Susssiest/Nornir-Chest-Project/All CAD/All STEPS/Stalagmite_2.step

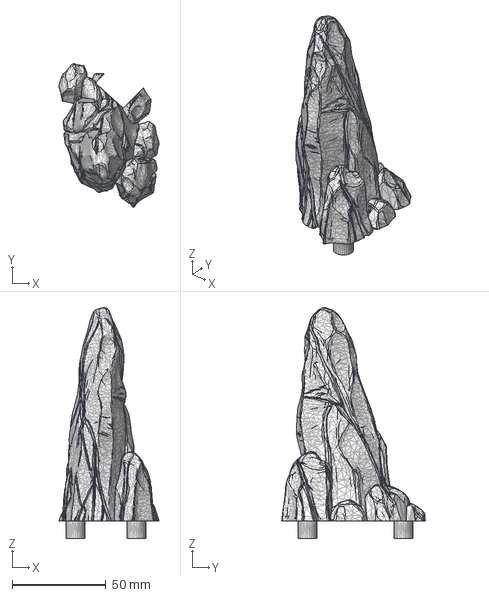
[picture p15: CAD file, 2026-08-25]
All CAD/All STEPS/Stalagmite_2.step
53.3 x 76.5 x 123.0 mm
