Susssiest/Nornir-Chest-Project/All CAD/All STEPS/Rune_Cylinder.step

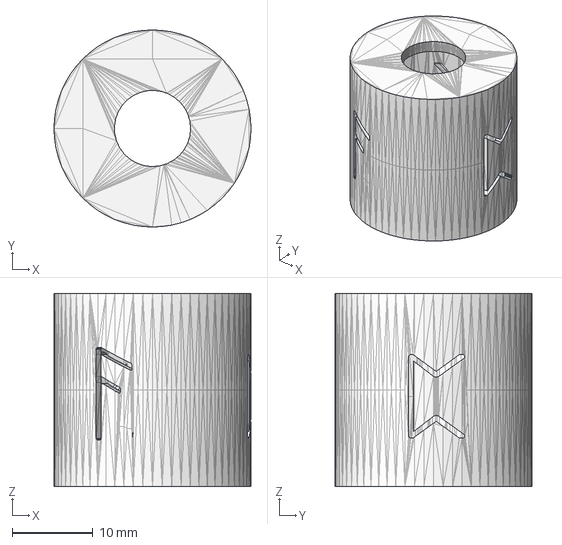
[picture p16: CAD file, 2026-08-25]
All CAD/All STEPS/Rune_Cylinder.step
24.4 x 24.4 x 23.9 mm
