Susssiest/Nornir-Chest-Project/All CAD/All STEPS/LED_Cover_(Totem_Pole).step

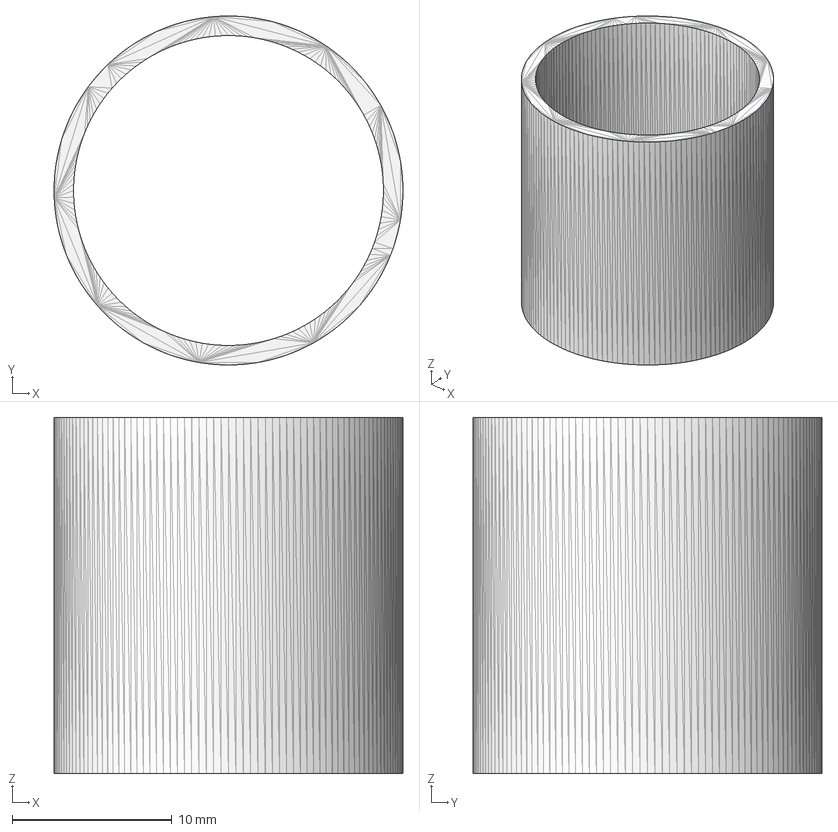
[picture p17: CAD file, 2026-08-25]
All CAD/All STEPS/LED_Cover_(Totem_Pole).step
21.8 x 21.8 x 22.3 mm
