Susssiest/Nornir-Chest-Project/All CAD/All STEPS/Totem_Pole.step

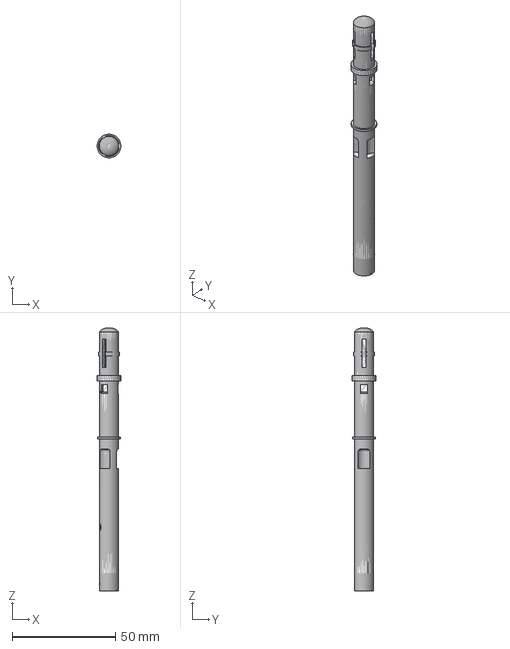
[picture p18: CAD file, 2026-08-25]
All CAD/All STEPS/Totem_Pole.step
11.5 x 11.5 x 127.4 mm
