Susssiest/Nornir-Chest-Project/All CAD/All STEPS/Gold_Engraving_Long PRINT_4.step

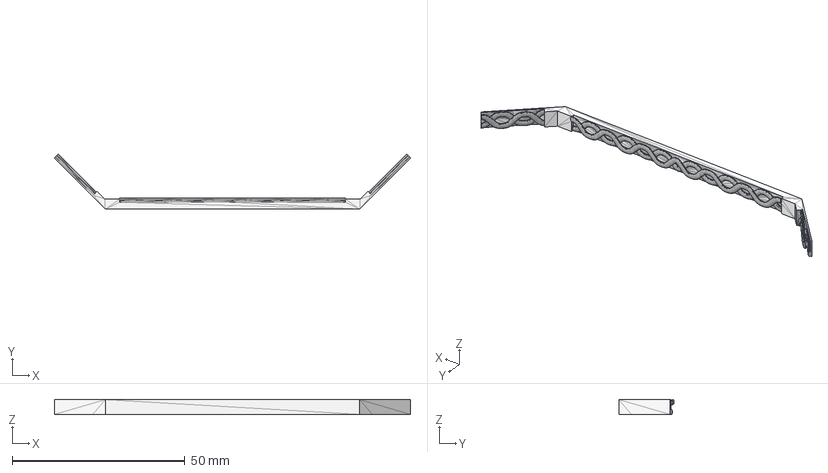
[picture p19: CAD file, 2026-08-25]
All CAD/All STEPS/Gold_Engraving_Long PRINT_4.step
103.2 x 16.0 x 4.30 mm
