Susssiest/Nornir-Chest-Project/All CAD/All STEPS/Hing_PRINT_2.step

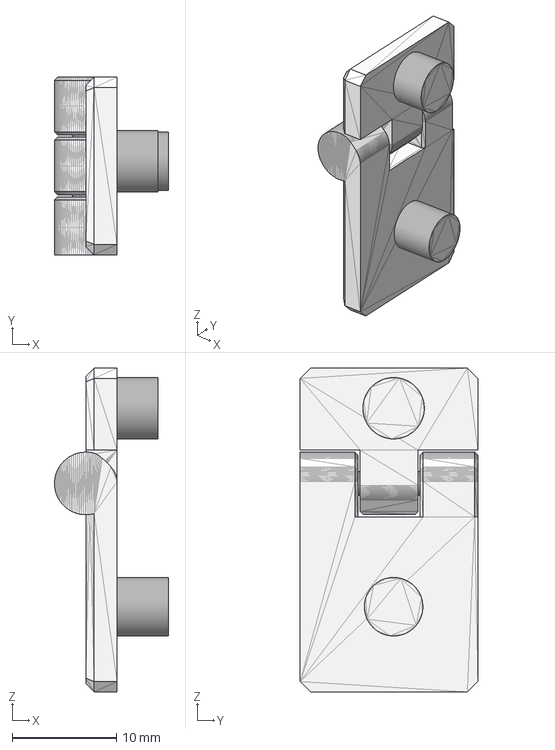
[picture p20: CAD file, 2026-08-25]
All CAD/All STEPS/Hing_PRINT_2.step
10.9 x 17.0 x 31.1 mm
