Susssiest/Nornir-Chest-Project/All CAD/All STEPS/Brazier_Rune_(R).step

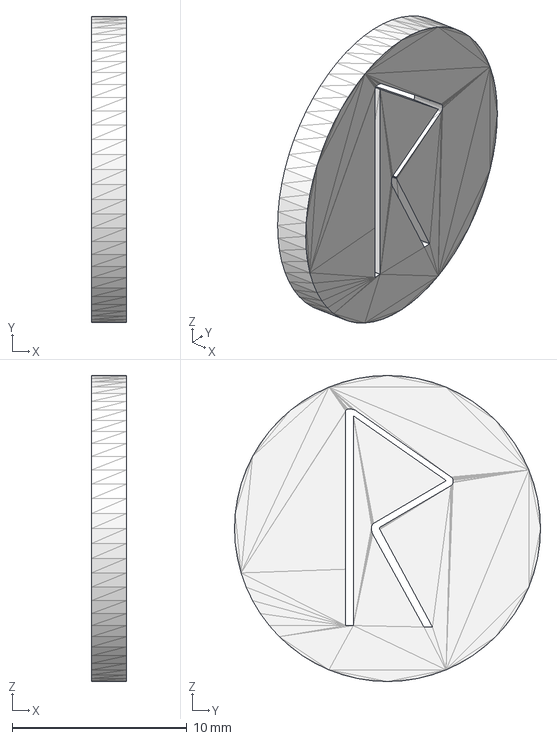
[picture p21: CAD file, 2026-08-25]
All CAD/All STEPS/Brazier_Rune_(R).step
2.00 x 17.5 x 17.5 mm
