Susssiest/Nornir-Chest-Project/All CAD/All STEPS/Base_Cover.step

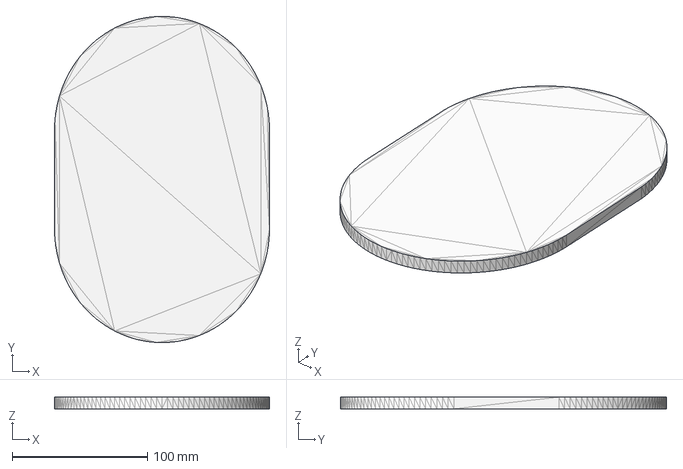
[picture p22: CAD file, 2026-08-25]
All CAD/All STEPS/Base_Cover.step
158.7 x 240.8 x 8.63 mm
