Susssiest/Nornir-Chest-Project/All CAD/All STEPS/Base_4.step

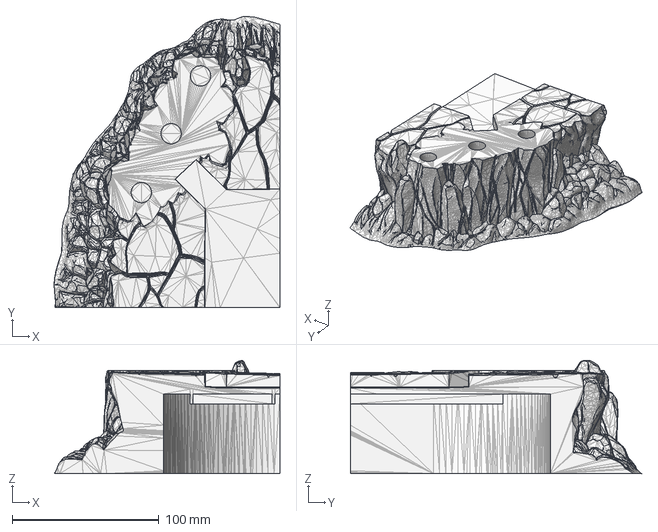
[picture p23: CAD file, 2026-08-25]
All CAD/All STEPS/Base_4.step
154.1 x 198.7 x 77.3 mm
