Susssiest/Nornir-Chest-Project/All CAD/All STEPS/Gold_Engraving_(Lid).step

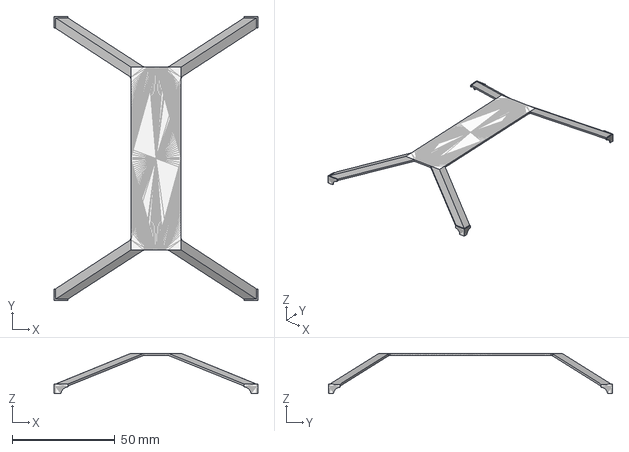
[picture p24: CAD file, 2026-08-25]
All CAD/All STEPS/Gold_Engraving_(Lid).step
99.3 x 138.4 x 19.7 mm
