Susssiest/Nornir-Chest-Project/All CAD/All STEPS/Lid.step

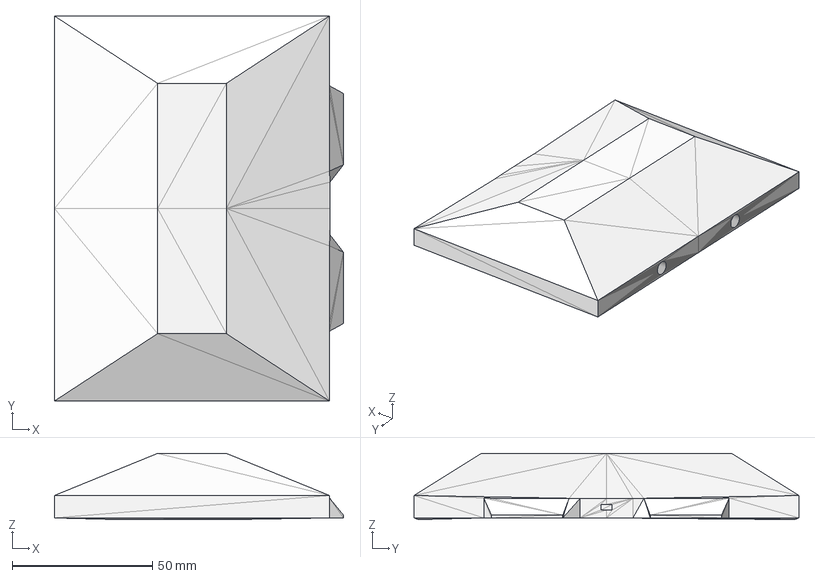
[picture p25: CAD file, 2026-08-25]
All CAD/All STEPS/Lid.step
103.0 x 137.2 x 23.6 mm
