Susssiest/Nornir-Chest-Project/All CAD/All STEPS/Pole_Target Print_3.step

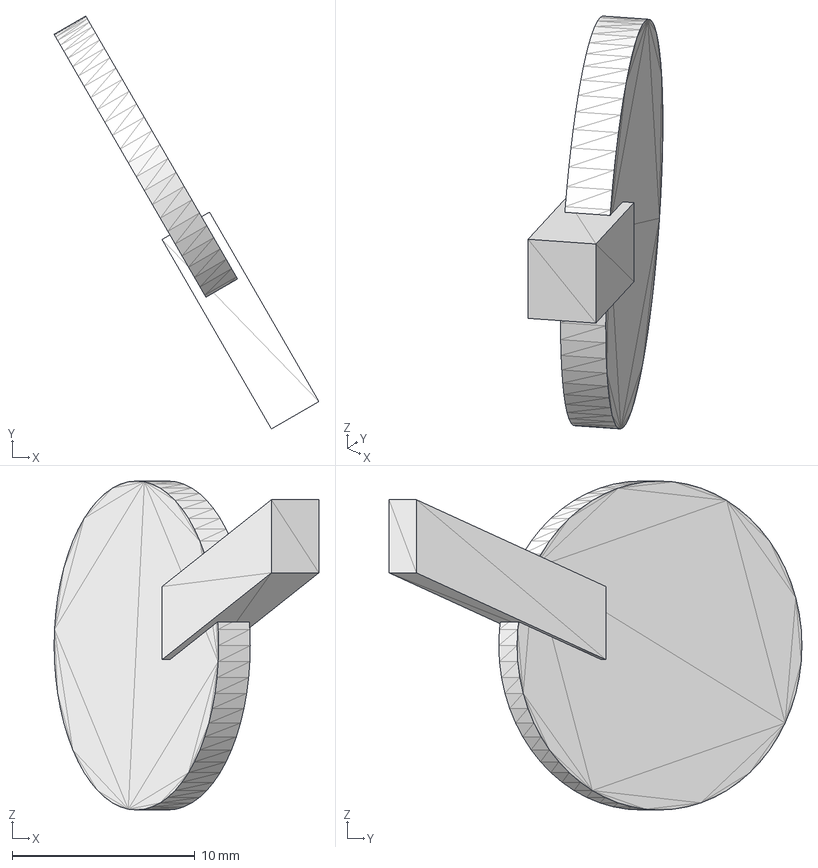
[picture p26: CAD file, 2026-08-25]
All CAD/All STEPS/Pole_Target Print_3.step
14.5 x 22.6 x 18.0 mm
