Susssiest/Nornir-Chest-Project/All CAD/All STEPS/Electronics_Cover.step

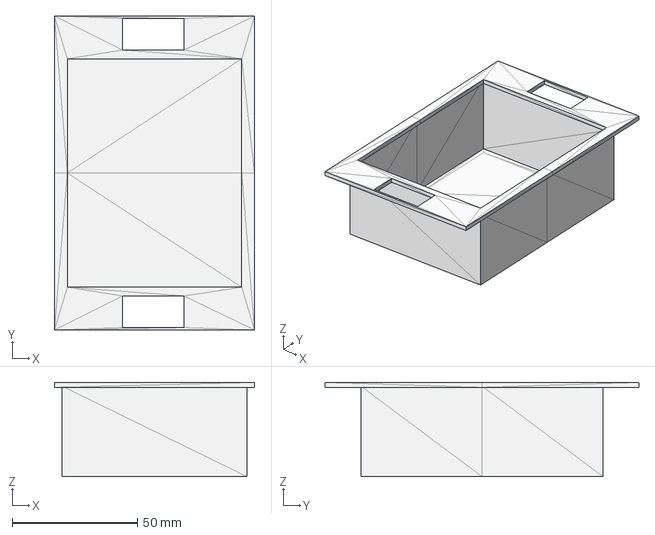
[picture p27: CAD file, 2026-08-25]
All CAD/All STEPS/Electronics_Cover.step
79.9 x 125.4 x 37.7 mm
