Susssiest/Nornir-Chest-Project/All CAD/All STEPS/Led_Cover_Print_3.step

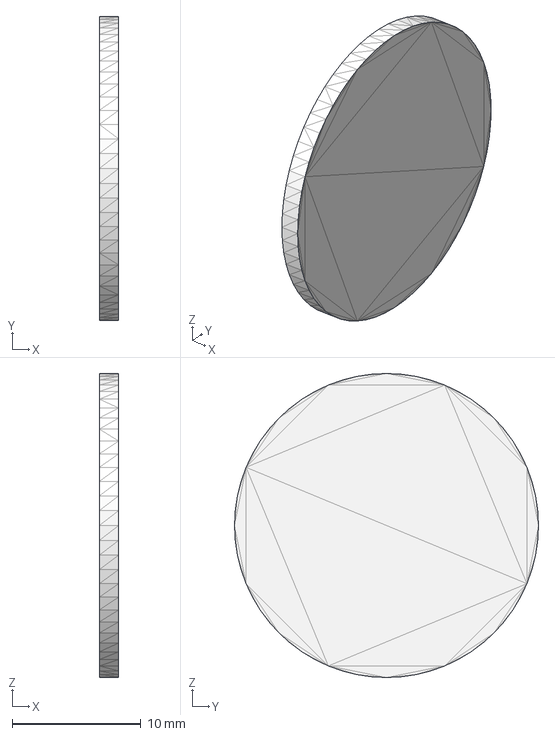
[picture p28: CAD file, 2026-08-25]
All CAD/All STEPS/Led_Cover_Print_3.step
1.50 x 23.6 x 23.6 mm
