Susssiest/Nornir-Chest-Project/All CAD/All STEPS/Ring_Print_3.step

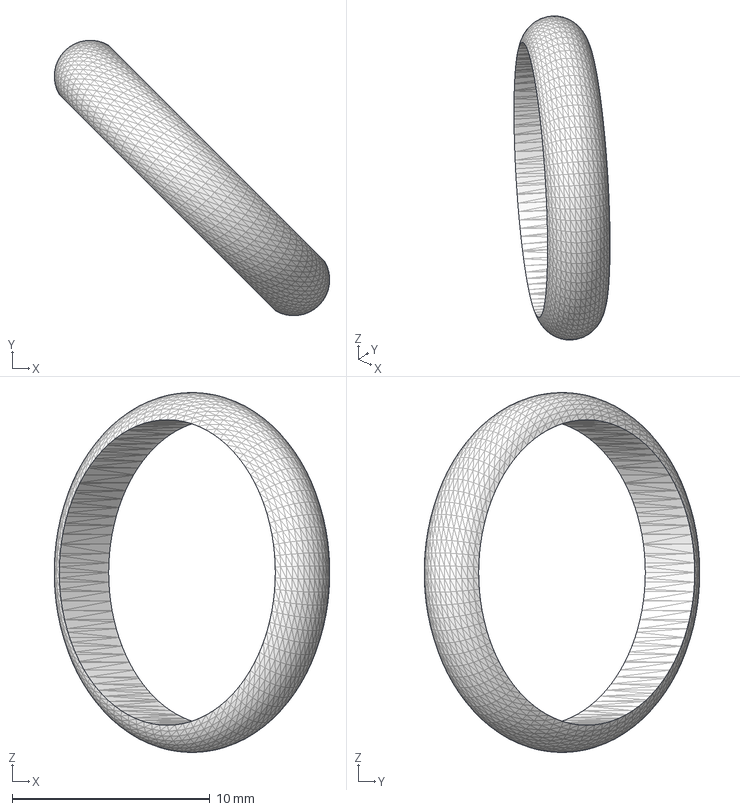
[picture p29: CAD file, 2026-08-25]
All CAD/All STEPS/Ring_Print_3.step
13.9 x 13.9 x 18.2 mm
