Susssiest/Nornir-Chest-Project/All CAD/All STEPS/Bottom.step

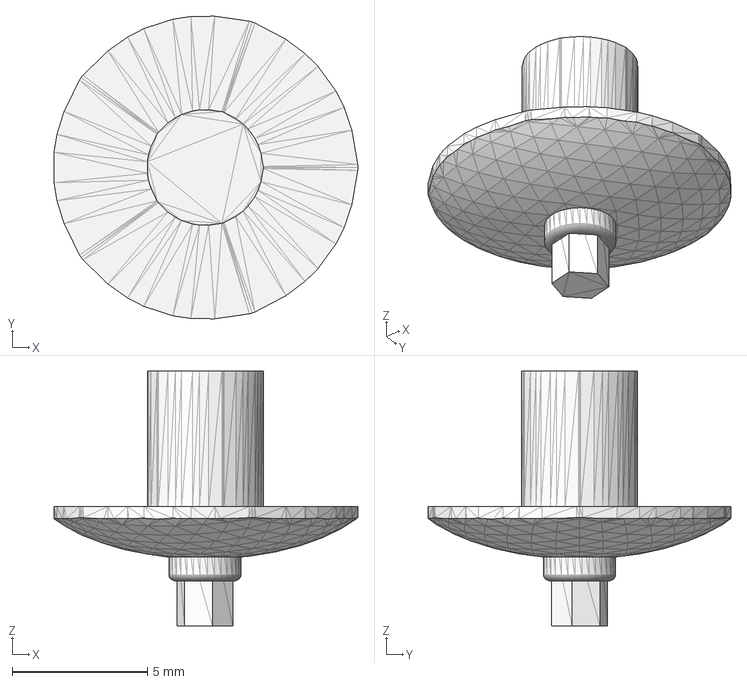
[picture p30: CAD file, 2026-08-25]
All CAD/All STEPS/Bottom.step
11.2 x 11.2 x 9.42 mm
