Susssiest/Nornir-Chest-Project/All CAD/All STEPS/Bell_Support.step

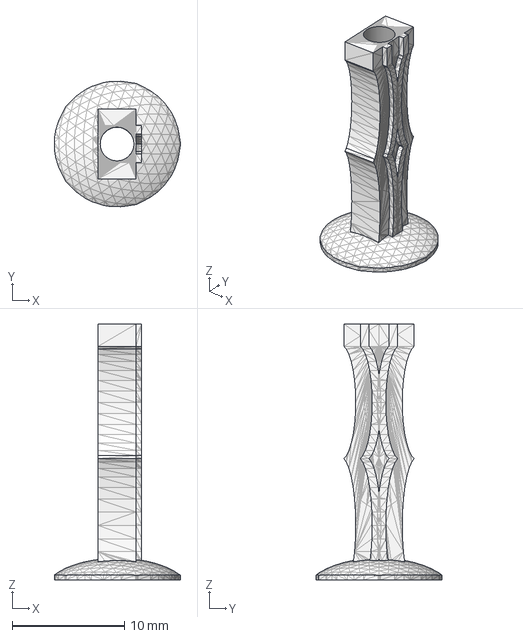
[picture p31: CAD file, 2026-08-25]
All CAD/All STEPS/Bell_Support.step
11.2 x 11.2 x 22.8 mm
