Susssiest/Nornir-Chest-Project/All CAD/All STEPS/Bell_Rune_(N).step

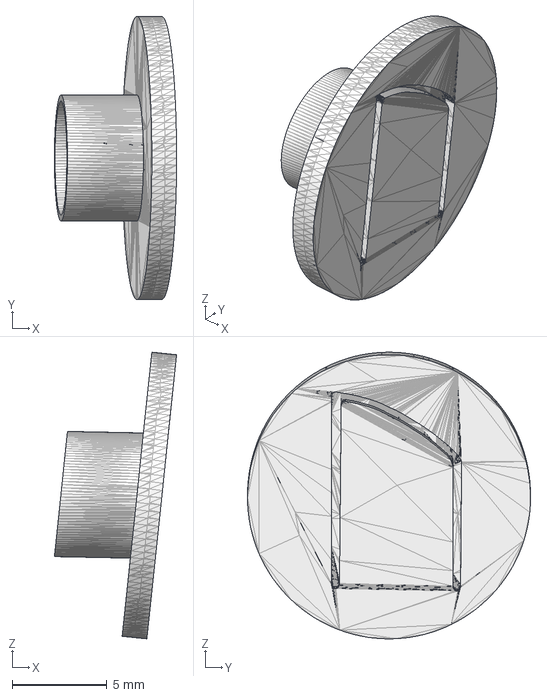
[picture p32: CAD file, 2026-08-25]
All CAD/All STEPS/Bell_Rune_(N).step
6.43 x 14.9 x 15.1 mm
