Susssiest/Nornir-Chest-Project/All CAD/All STEPS/Stand_Pin.step

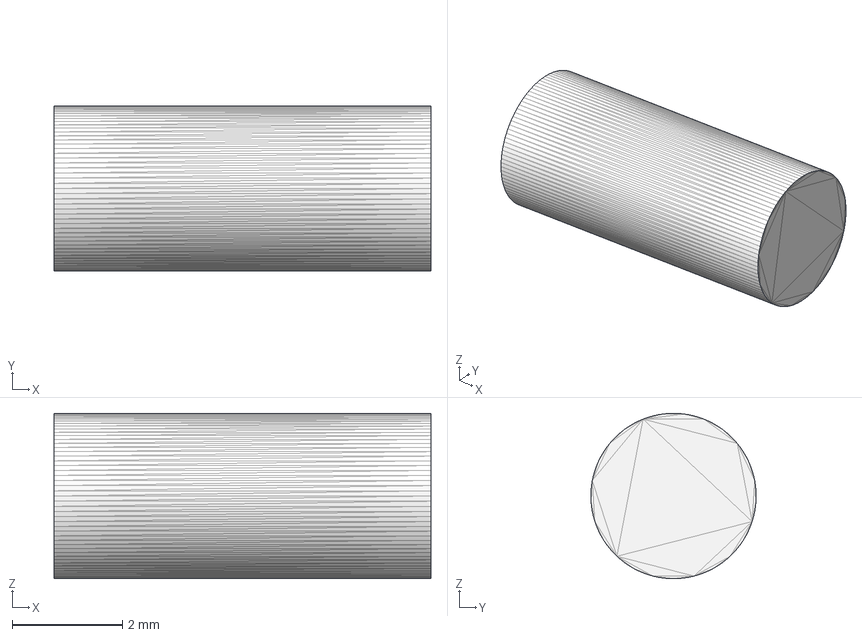
[picture p33: CAD file, 2026-08-25]
All CAD/All STEPS/Stand_Pin.step
6.84 x 3.00 x 3.00 mm
