Susssiest/Nornir-Chest-Project/All CAD/All STEPS/Brazier_Rune_Cover.step

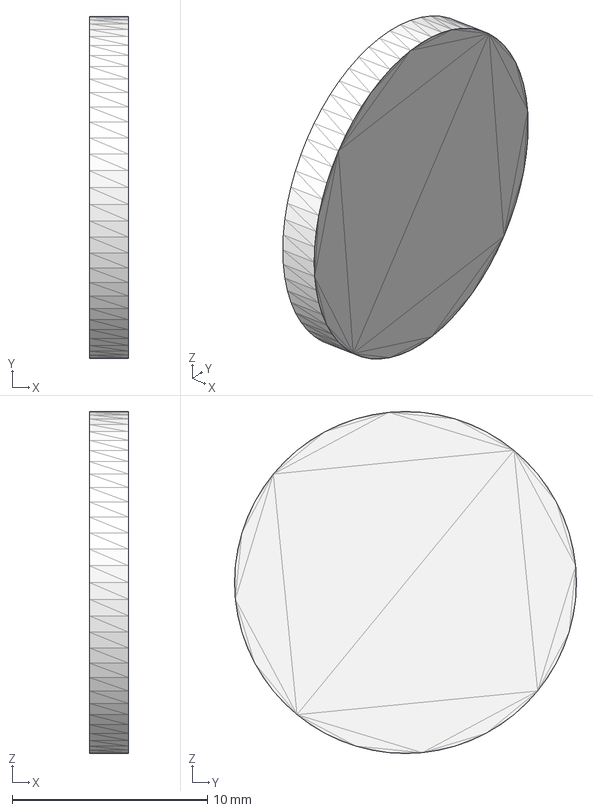
[picture p34: CAD file, 2026-08-25]
All CAD/All STEPS/Brazier_Rune_Cover.step
2.00 x 17.5 x 17.5 mm
